Rashid36016/Reverse-vending-machine-with-Double-Shaft-Shredder-by-Machine-Learning/3D Parts/3D STL file/Setup.png

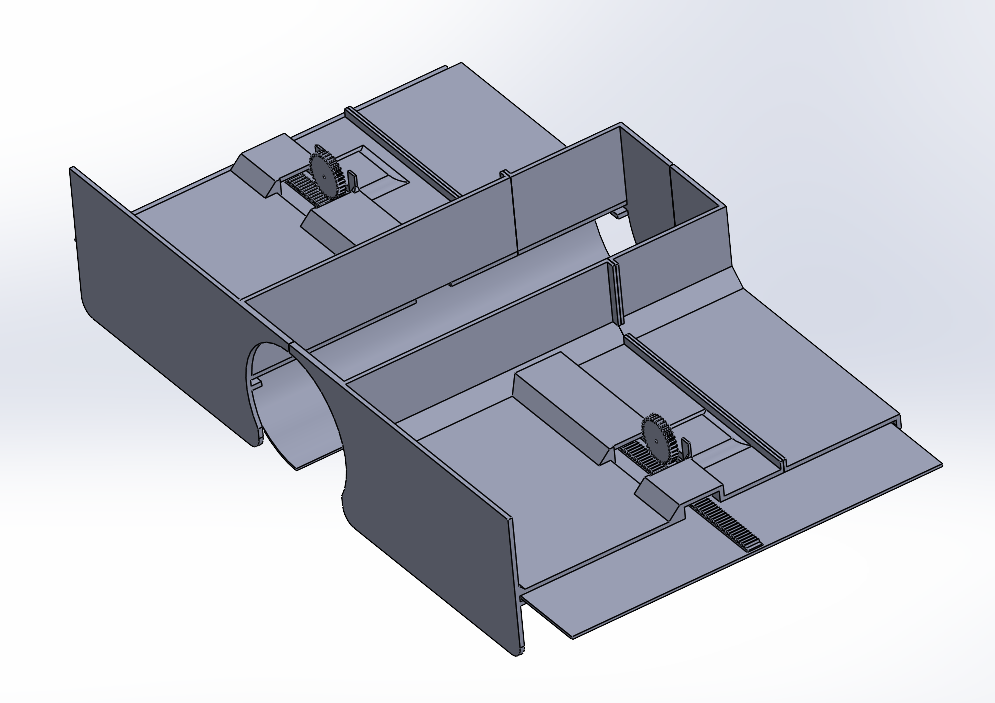
3D Parts/3D STL file/Setup.png
