Rashid36016/Reverse-vending-machine-with-Double-Shaft-Shredder-by-Machine-Learning/AI (YOLO) model/YOLO model/stream_test.py

import cv2
import numpy as np
import requests

# ========= CHANGE IP IF NEEDED =========
url = "http://192.168.0.112/stream"
# =======================================

print("Connecting to ESP32 stream...")

stream = requests.get(url, stream=True)

bytes_data = b""

for chunk in stream.iter_content(chunk_size=1024):
    bytes_data += chunk

    a = bytes_data.find(b'\xff\xd8')  # JPEG start
    b = bytes_data.find(b'\xff\xd9')  # JPEG end

    if a != -1 and b != -1:
        jpg = bytes_data[a:b+2]
        bytes_data = bytes_data[b+2:]

        img = cv2.imdecode(np.frombuffer(jpg, dtype=np.uint8), cv2.IMREAD_COLOR)

        if img is not None:
            cv2.imshow("ESP32 Stream", img)

        if cv2.waitKey(1) & 0xFF == 27:
            break

cv2.destroyAllWindows()
